svenpetersen1965/Pi1541-HAT/Pi1541/Pi1541-Switch/Rev. 1/Text/112_COVER_SHEET.docx

Documentation

Pi1541 - Switch

Project number: 112

Revision: 1

Date: 26.02.2019
