svenpetersen1965/Pi1541-HAT/Pi1541/Pi1541-HAT/Rev. 2/pictures/1746_-_Pi1541_case_open.JPG

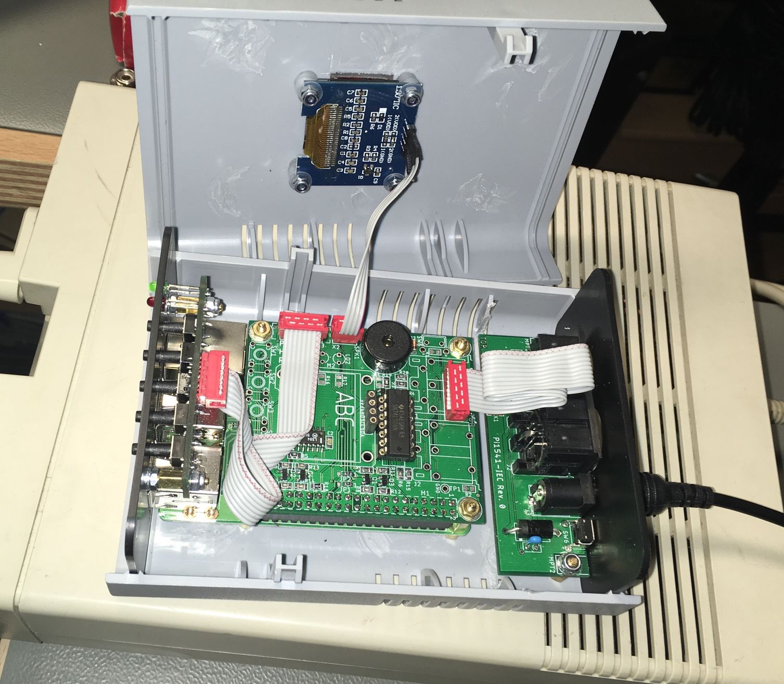
Pi1541/Pi1541-HAT/Rev. 2/pictures/1746_-_Pi1541_case_open.JPG
