svenpetersen1965/Pi1541-HAT/Pi1541/Pi1541-Rot/Rev. 0/pictures/CCW_100k.png

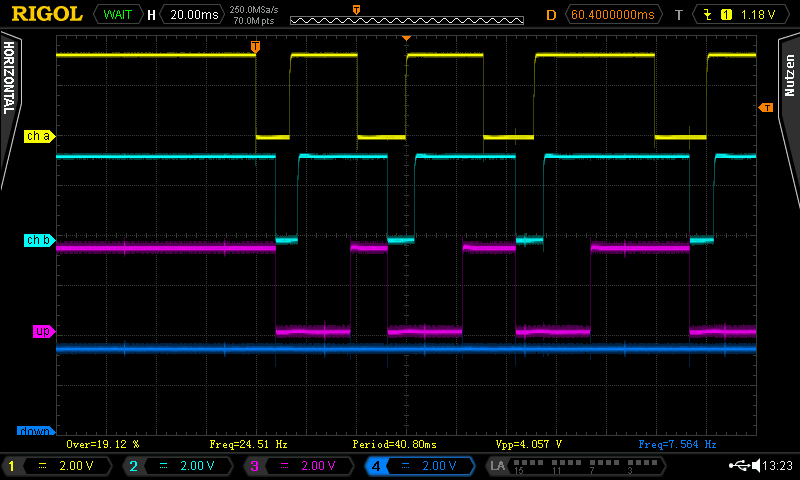
Pi1541/Pi1541-Rot/Rev. 0/pictures/CCW_100k.png
