svenpetersen1965/Pi1541-HAT/Pi1541/Pi1541-HAT/Rev. 2/pictures/Max_Curr_test_20190323.jpg

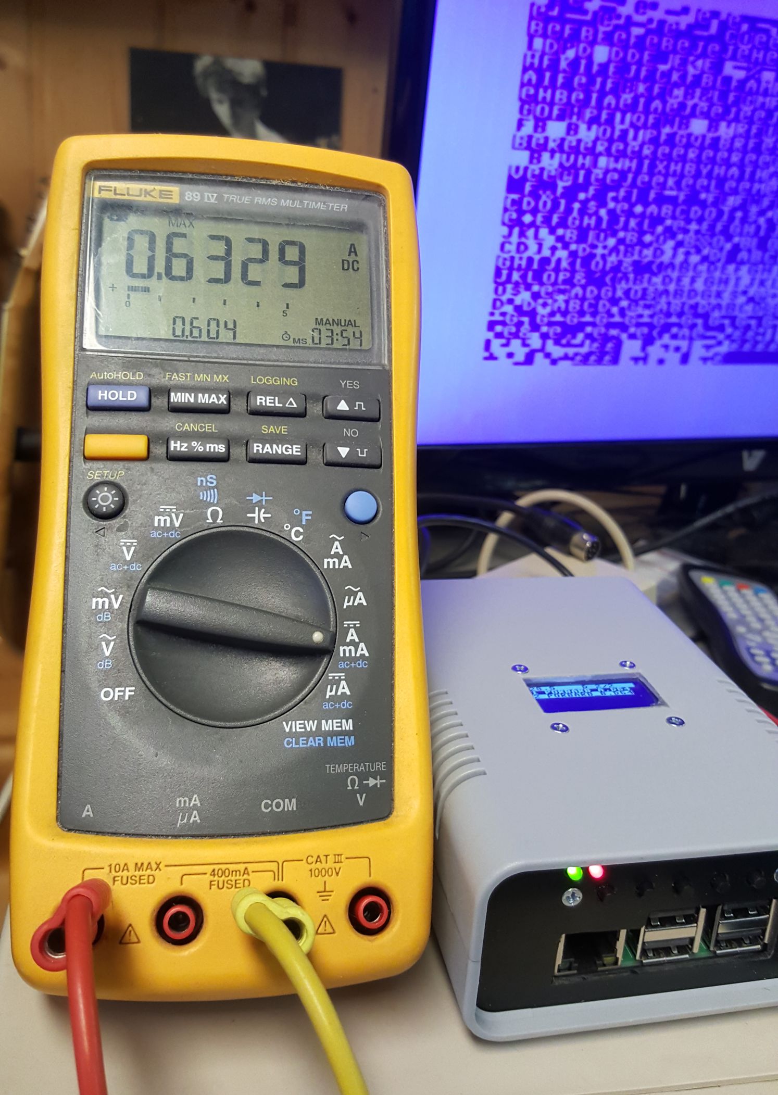
Pi1541/Pi1541-HAT/Rev. 2/pictures/Max_Curr_test_20190323.jpg
