svenpetersen1965/Pi1541-HAT/Pi1541/Pi1541-HAT/Rev. 2/pictures/Pi1541_HAT_measures.png

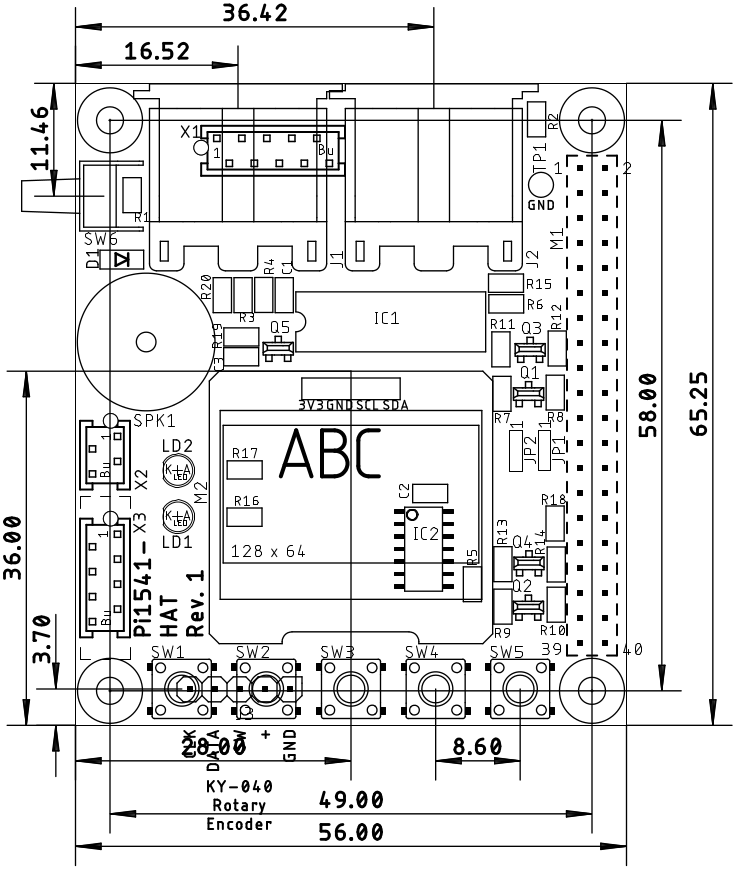
Pi1541/Pi1541-HAT/Rev. 2/pictures/Pi1541_HAT_measures.png
