svenpetersen1965/Pi1541-HAT/Pi1541/Pi1541-Rot/Rev. 0/pictures/1789_-_Testing.jpg

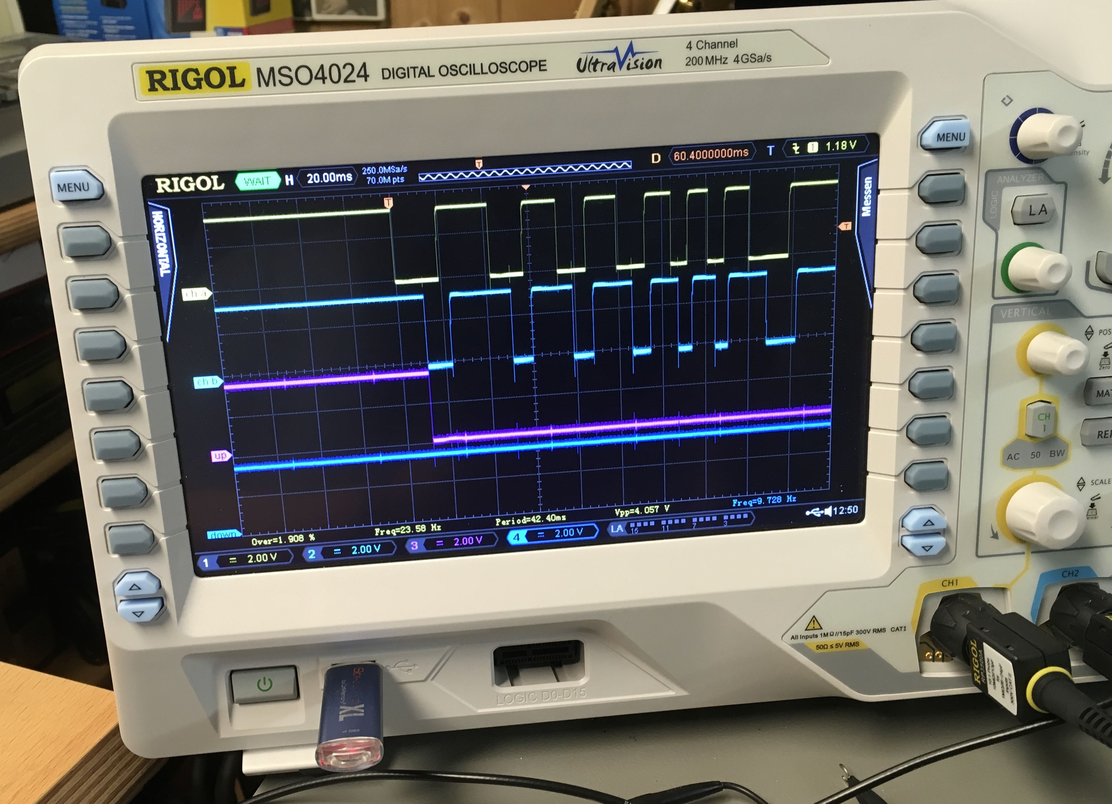
Pi1541/Pi1541-Rot/Rev. 0/pictures/1789_-_Testing.jpg
