svenpetersen1965/Pi1541-HAT/Pi1541/Pi1541-IEC/Rev. 0/pdf/Pi1541-IEC_v0.pdf

# Project Documentation

Pi1541-IEC

## Project number: 115

Revision: 0

## Date: 27.02.2019

Pi1541-IEC_ModB_v0.docx 27.02.2019 13:28 Drafted by Sven Petersen Page 1 of 1 Doc.-No.: 115-6-01-00

## Pi1541-IEC Rev. 0 Module Description

Description
The Pi1541-IEC serves the Pi1541-HAT (project number 111) as an optional break out board for the IEC connectors. It also contains a barrel connector (5,5/2,5mm) for an alternative power supply connection plus an overvoltage protection. A reset switch for the IEC-bus can be placed. A ribbon cable plus a MicroMatch connector provide the connection to the Pi1541-
HAT.

Pinouts
IEC-Bus
J1 and J2 – Lumberg 010599 06, 6p DIN receptables
Pin Signal
1 /SRQ (not used in this design)

### 2 GND

### 3 ATN

### 4 CLK

### 5 DATA

6 /RESET

IEC Bus (to Pi1541 HAT)
X1 – 10p Micro Match receptible, female, vertical, through hole, e.g. MPE Garry 369-1-010
Pin Signal
1 /SRQ (not used in this design)

### 2 GND

### 3 ATN

### 4 CLK

### 5 DATA

6 /RESET
10 GND

7 +5V
8 +5V

### 9 GND

+5VDC Power
5,5mm/2,5mm barrel connector Pin Signal
Center +5VDC
Shaft GND

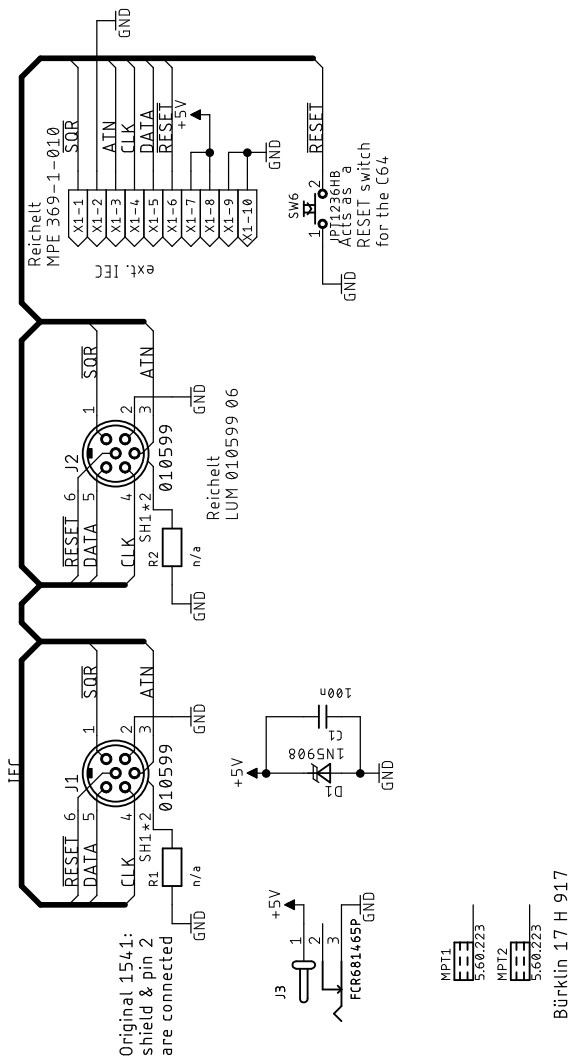
[picture p83: page 3]

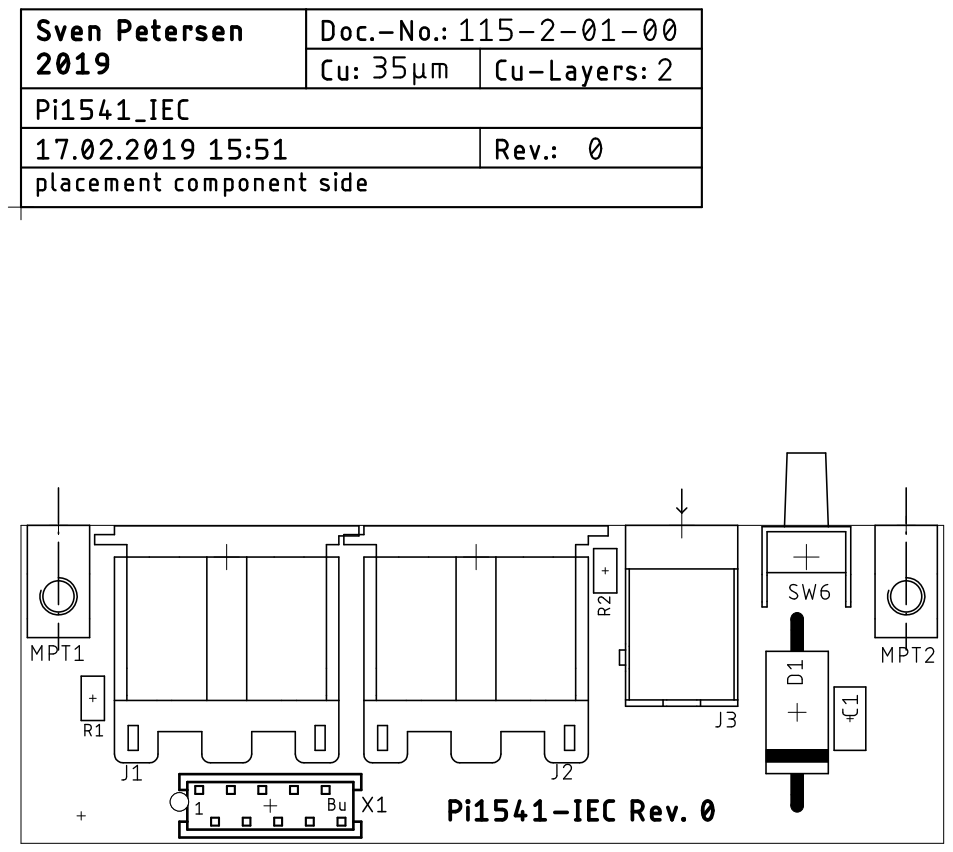
[picture p84: page 4]

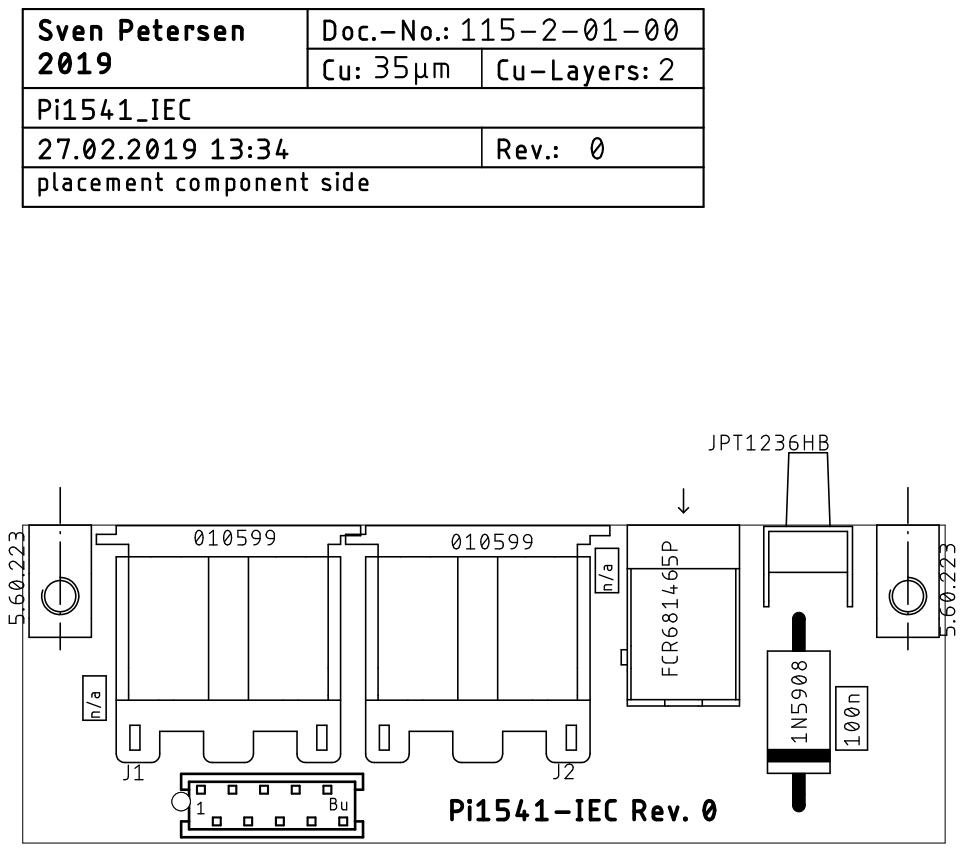
[picture p85: page 5]

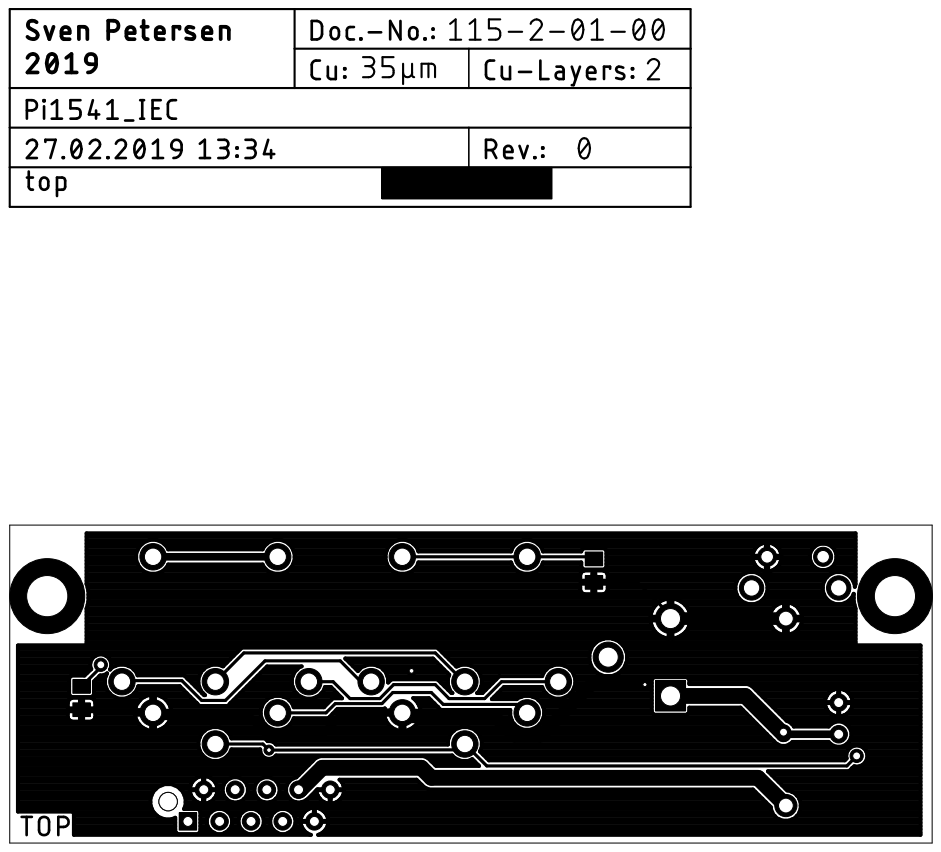
[picture p86: page 6]

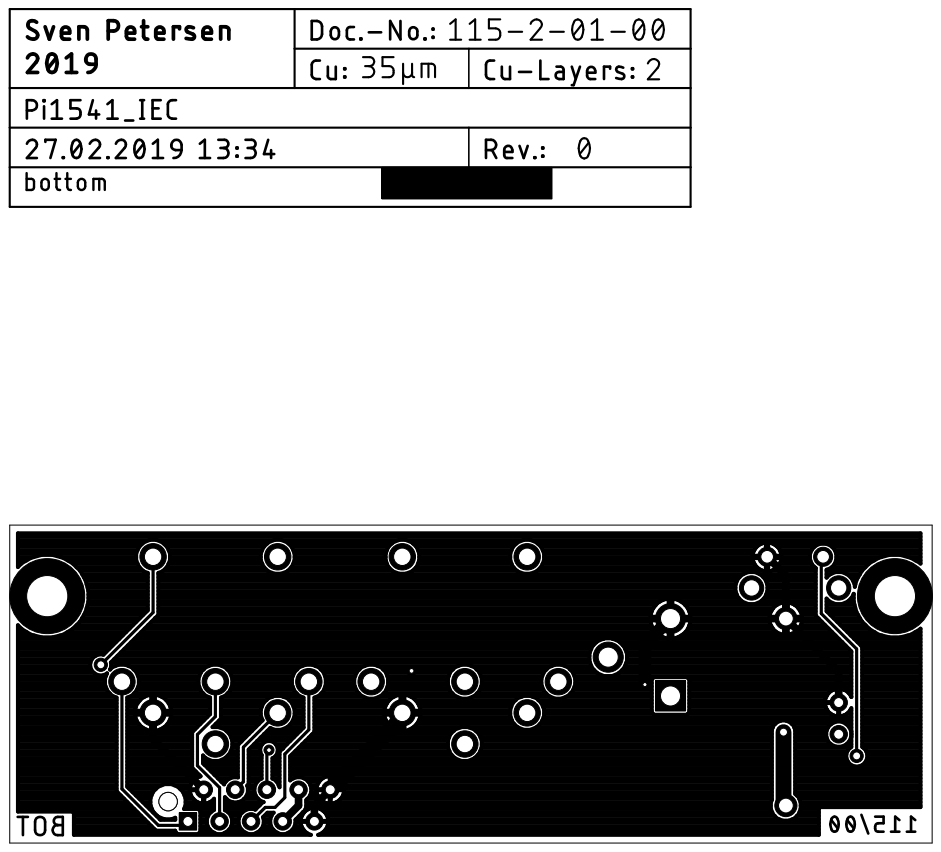
[picture p87: page 7]

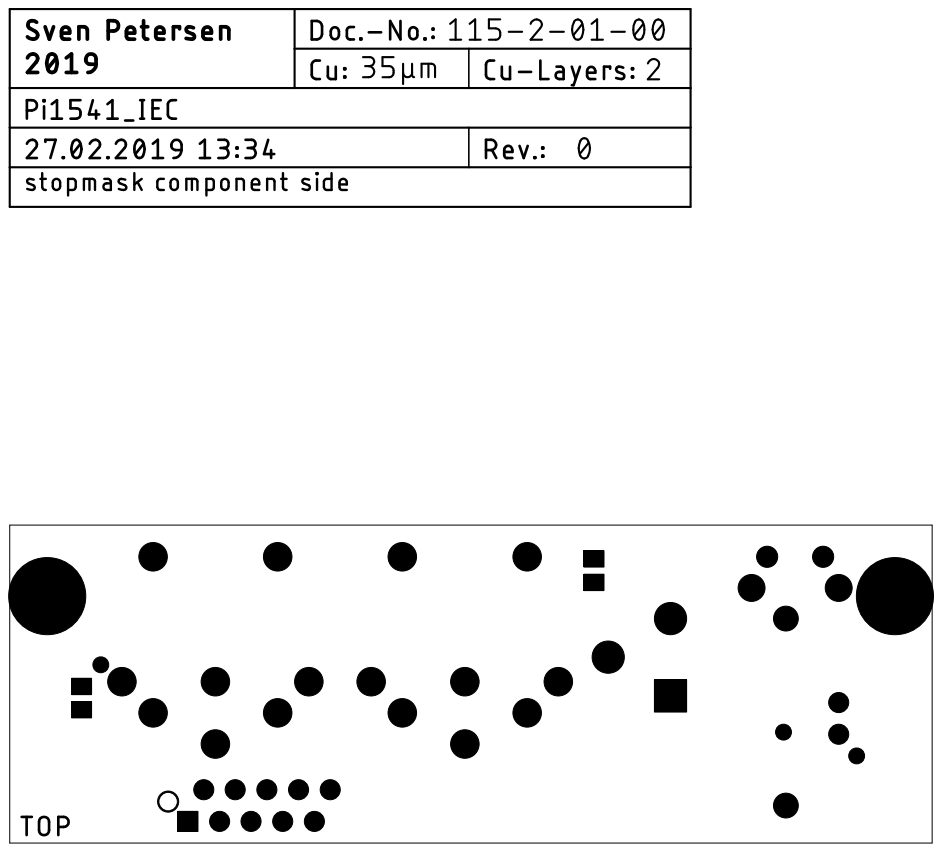
[picture p88: page 8]

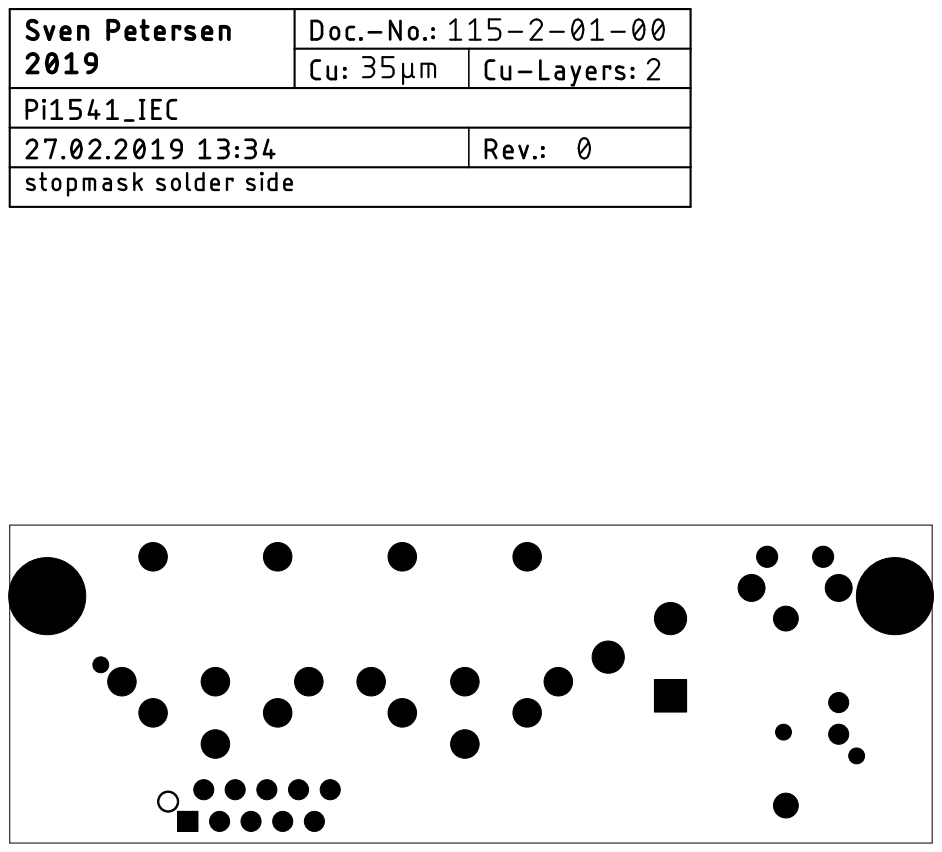
[picture p89: page 9]

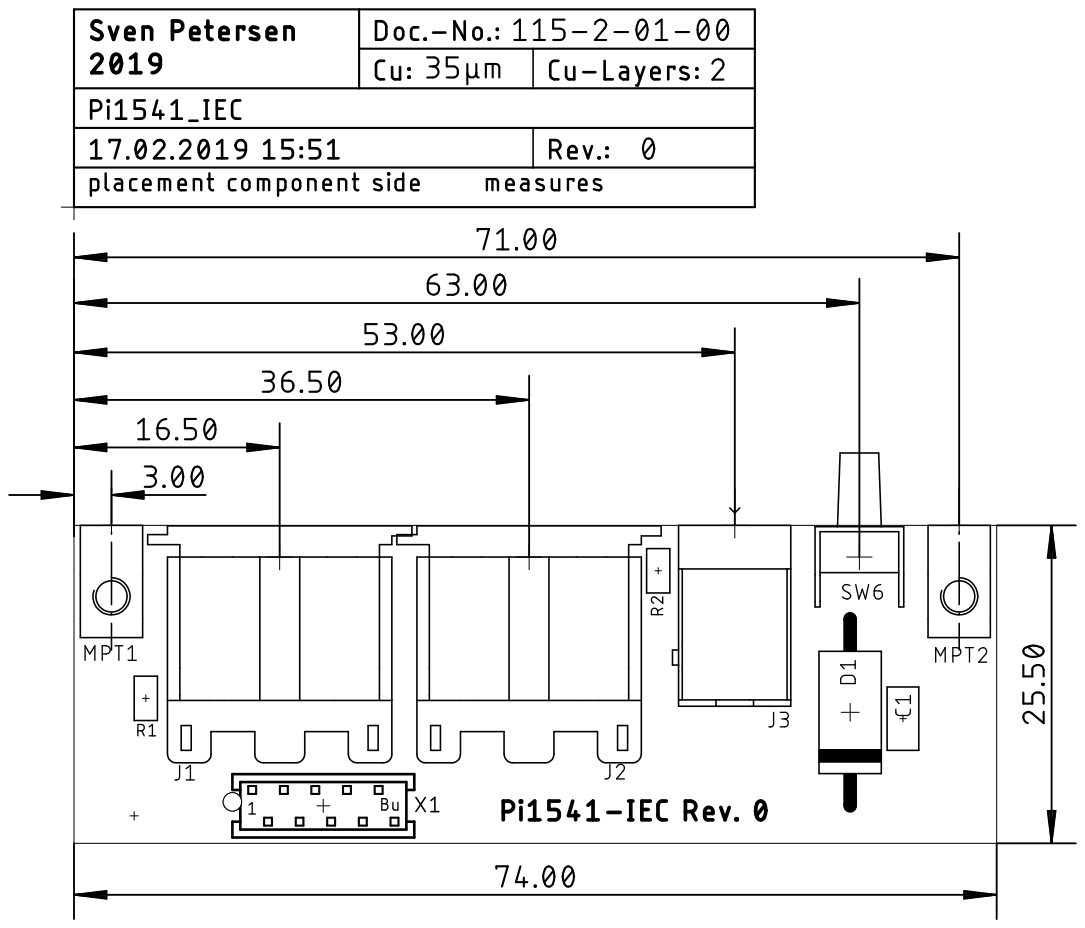
[picture p90: page 10]

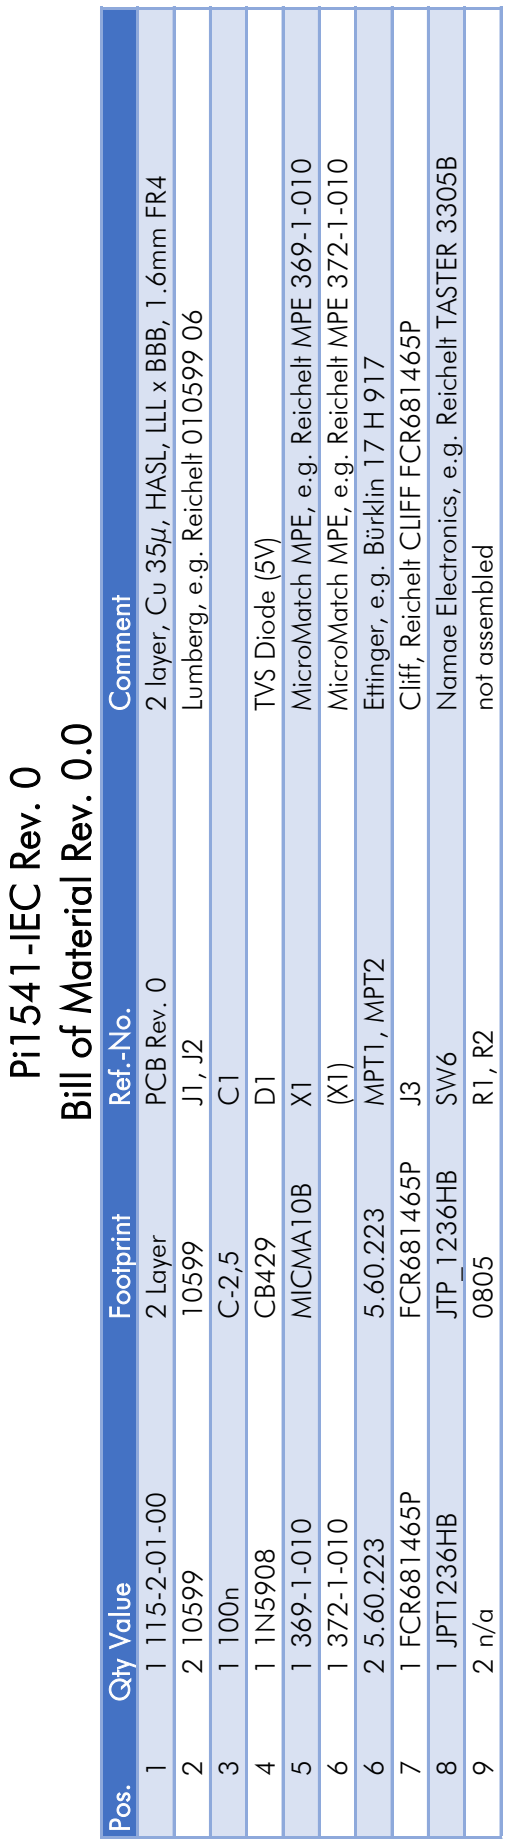
[picture p91: figure]
4 1 1N5908 CB429 D1 TVS Diode (5V) 9 2 n/a 0805 R1, R2 not assembled

Pos. Qty Value Footprint Ref.-No. Comment

1 1 115-2-01-00 2 Layer PCB Rev. 0 2 layer, Cu 35µ, HASL, LLL x BBB, 1.6mm FR4
2 2 10599 10599 J1, J2 Lumberg, e.g. Reichelt 010599 06

3 1 100n C-2,5 C1

5 1 369-1-010 MICMA10B X1 MicroMatch MPE, e.g. Reichelt MPE 369-1-010

6 1 372-1-010 (X1) MicroMatch MPE, e.g. Reichelt MPE 372-1-010
6 2 5.60.223 5.60.223 MPT1, MPT2 Ettinger, e.g. Bürklin 17 H 917

7 1 FCR681465P FCR681465P J3 Cliff, Reichelt CLIFF FCR681465P

8 1 JPT1236HB JTP_1236HB SW6 Namae Electronics, e.g. Reichelt TASTER 3305B

Pi1541-IEC Rev. 0

Bill of Material Rev. 0.0

Pi1541-IEC_BOM_v0_0.xlsx

Drafted by Sven Petersen Page 1 of 1

27.02.2019 14:09
Doc.No.: 115-5-01-00.0
